t3ry4git/stm32Co2/test.ioc

Mcu.UserName=STM32F103C8Tx
PA10.Signal=USART1_RX
PA13.Signal=SYS_JTMS-SWDIO
PA14.Signal=SYS_JTCK-SWCLK
PA9.Signal=USART1_TX
PB6.Signal=I2C1_SCL
PB7.Signal=I2C1_SDA
PC13-TAMPER-RTC.GPIO_Label=boardLED
PC13-TAMPER-RTC.Signal=GPIO_Output
PD0-OSC_IN.Signal=RCC_OSC_IN
PD1-OSC_OUT.Signal=RCC_OSC_OUT
